SukkoPera/Raemixx500/doc/dimensions1.jpg

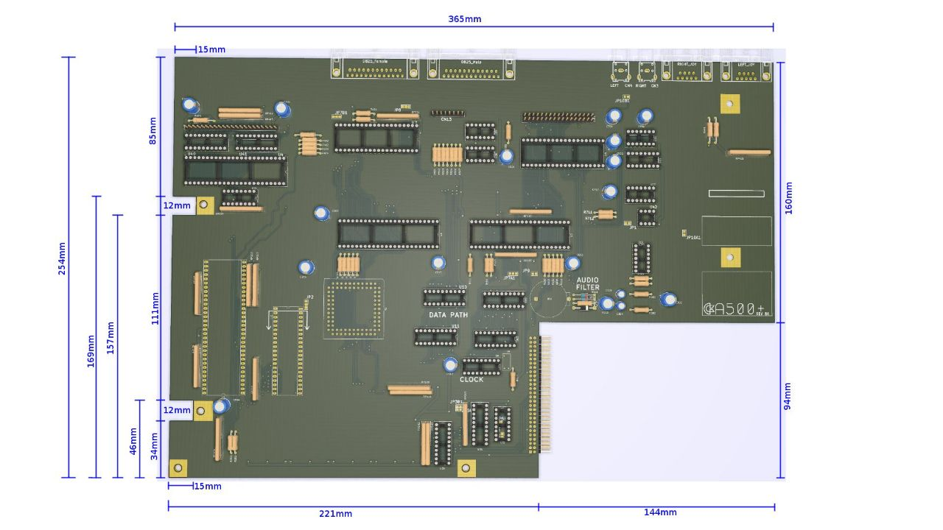
doc/dimensions1.jpg
